turtle-bazon/yolochka-remastered/case/export/yolochka-remastered-bumpon.step

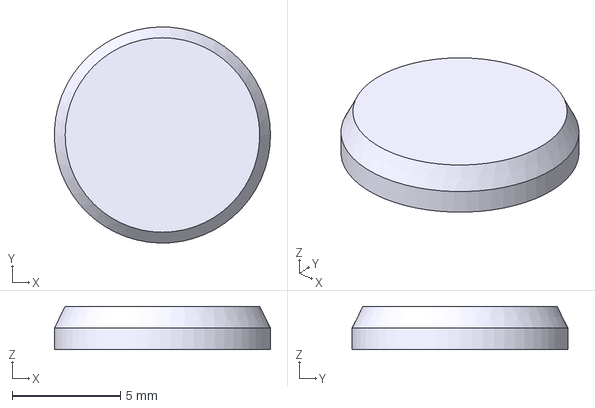
[picture p18: CAD file, 2026-01-16]
case/export/yolochka-remastered-bumpon.step
9.99 x 10.00 x 2.00 mm
