turtle-bazon/yolochka-remastered/pcb/yolochka_lib/3d/SuperMini_FlatConnector.step

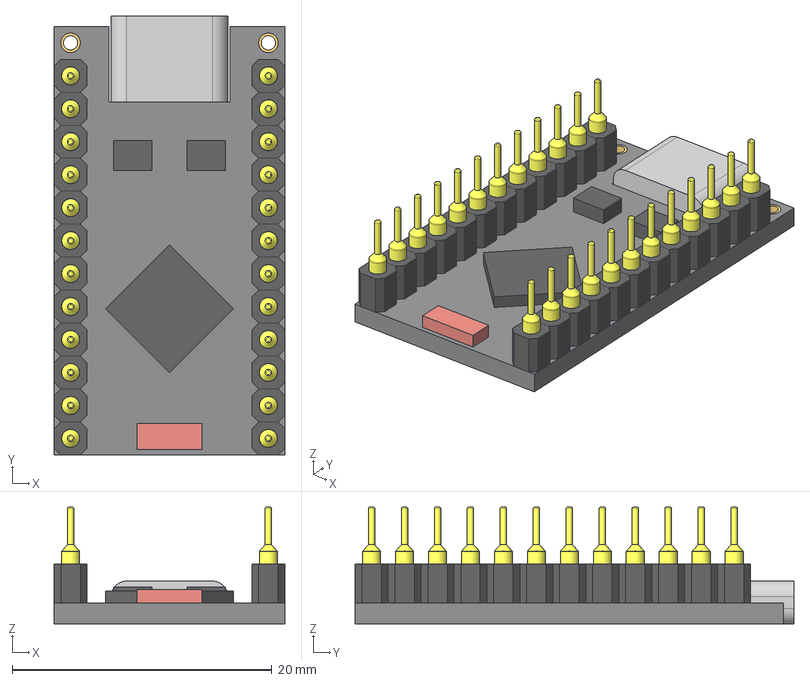
[picture p19: CAD file, 2026-01-05]
pcb/yolochka_lib/3d/SuperMini_FlatConnector.step
17.8 x 33.8 x 9.00 mm
SuperMini v1
SuperMini v002
SuperMini v003
SuperMini v004
SuperMini v005
SuperMini v006
SuperMini v007
SuperMini v008
SuperMini v009
SuperMini v010
SuperMini v011
SuperMini v012
SuperMini v013
SuperMini v014
SuperMini v015
SuperMini v016
SuperMini v017
SuperMini v018
SuperMini v019
SuperMini v020
SuperMini v021
SuperMini v022
SuperMini v023
SuperMini v024
SuperMini v025
SuperMini v026
SuperMini v027
SuperMini v028
SuperMini v029
SuperMini v030
SuperMini v031
SuperMini v032
SuperMini v033
female-header-1p-clone-for-12p x 12
female-header-1p-clone-for-12p001 x 12
female-header-1p-clone-for-12p036 x 12
female-header-1p-clone-for-12p037 x 12
