turtle-bazon/yolochka-remastered/case/export/yolochka-remastered-top.step

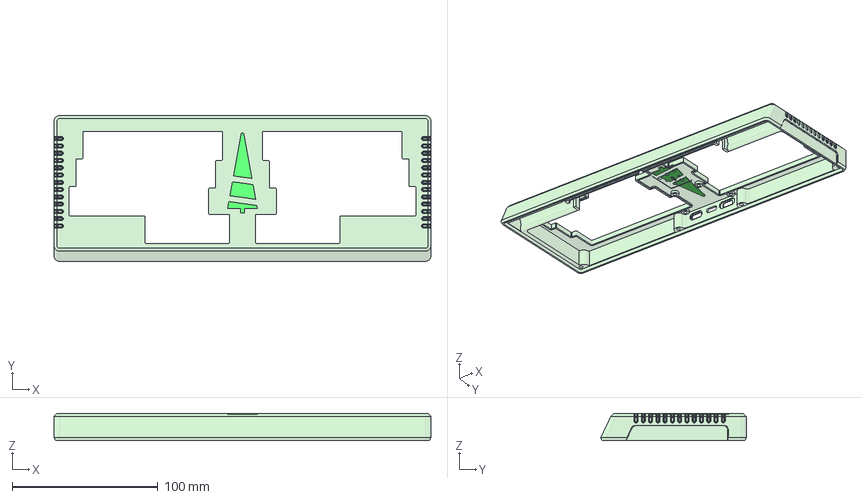
[picture p20: CAD file, 2026-01-16]
case/export/yolochka-remastered-top.step
259.1 x 100.1 x 18.6 mm
yolochka-on-top
top
