turtle-bazon/yolochka-remastered/pcb/yolochka_lib/3d/HotswapMX.stp

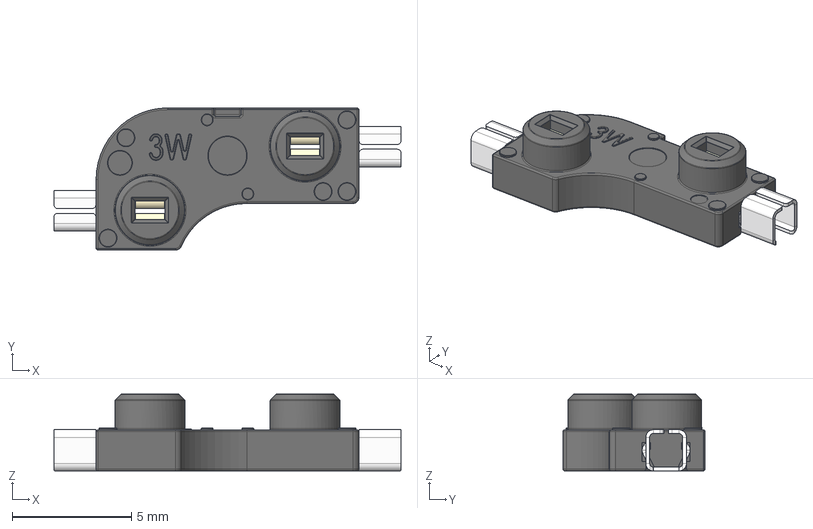
[picture p21: CAD file, 2026-01-05]
pcb/yolochka_lib/3d/HotswapMX.stp
14.5 x 5.95 x 3.22 mm
