turtle-bazon/yolochka-remastered/case/export/yolochka-remastered-switchplate.step

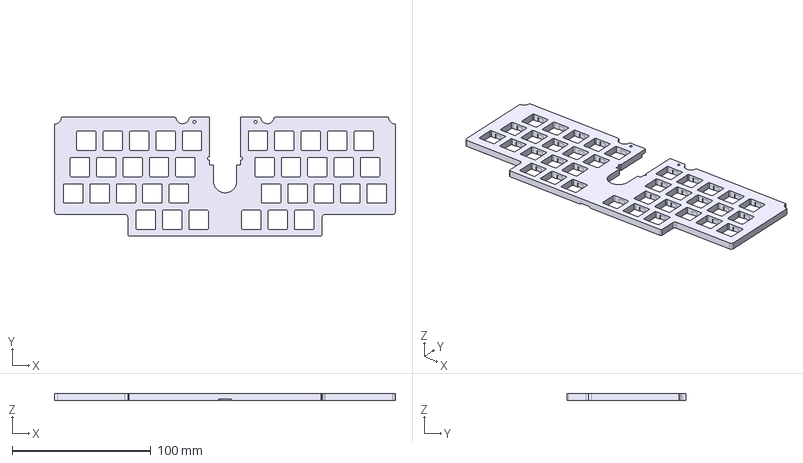
[picture p22: CAD file, 2026-01-16]
case/export/yolochka-remastered-switchplate.step
245.5 x 85.5 x 5.00 mm
