turtle-bazon/yolochka-remastered/case/export/yolochka-remastered-top-fill.step

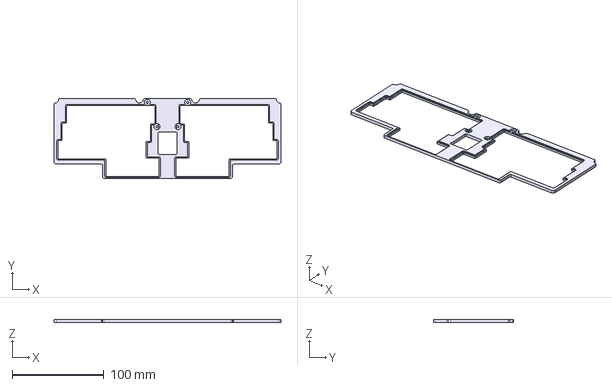
[picture p23: CAD file, 2026-01-16]
case/export/yolochka-remastered-top-fill.step
246.9 x 86.9 x 3.00 mm
