turtle-bazon/yolochka-remastered/case/export/yolochka-remastered-reset-button-pusher.step

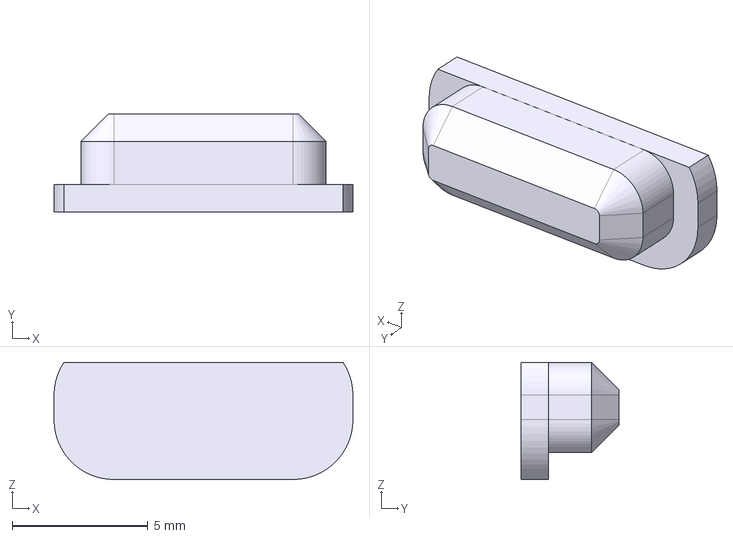
[picture p24: CAD file, 2026-01-16]
case/export/yolochka-remastered-reset-button-pusher.step
11.0 x 3.60 x 4.31 mm
