turtle-bazon/yolochka-remastered/case/export/yolochka-remastered-bottom-fill.step

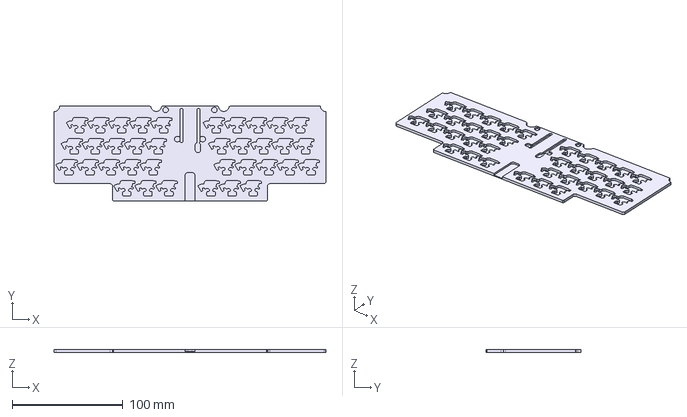
[picture p25: CAD file, 2026-01-16]
case/export/yolochka-remastered-bottom-fill.step
245.5 x 85.5 x 2.40 mm
